Equipe-Botcem/Seguidor_Lampedrao/Estrutura/bateria.SLDPRT

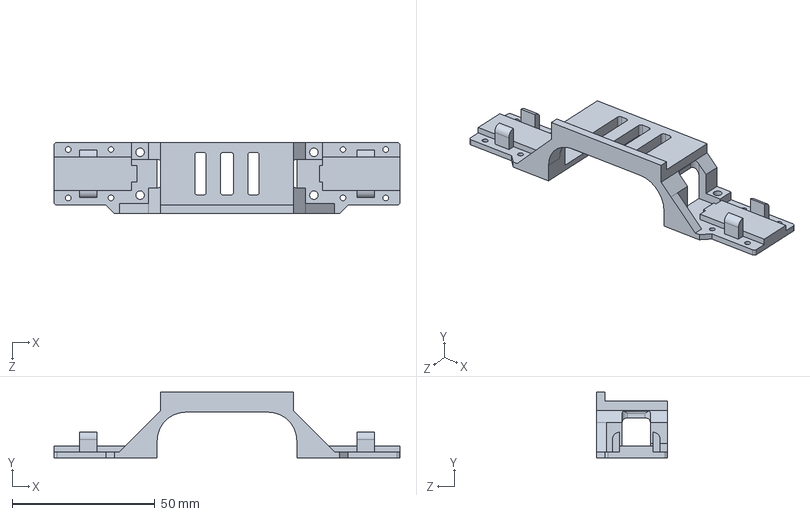
[picture p15: CAD file, 2023-05-12]
Estrutura/bateria.SLDPRT
121.4 x 23.0 x 25.0 mm
