Equipe-Botcem/Seguidor_Lampedrao/Elétrica/parts/1622242-1/1622242-1.step

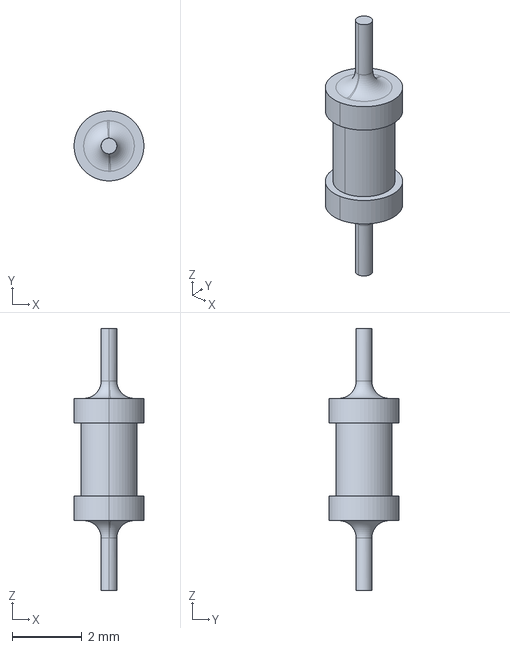
[picture p16: CAD file, 2023-05-12]
Elétrica/parts/1622242-1/1622242-1.step
2.00 x 2.00 x 7.50 mm
