Equipe-Botcem/Seguidor_Lampedrao/esp32_code/include/Sensor.h

#ifndef _SENSOR_
#define _SENSOR_
#define RESOLUTION 4095
#include "Arduino.h"

class Sensor
{
public:
	Sensor();
	Sensor(unsigned char pin);

	void Init();

	uint16_t Read_sensor();
	int Read_Calibrado();
	bool Read_histerese();

	void setAngle(float angulo);
	void find_max();	
	float Read_CalibradoPonderado();
	float GetMax();


	float Cmax = 0;
	float Cmin = 0;
	
	
private:
	unsigned char pin_sensor;
	float angle;

	enum estado{
		Preto = 0,
		Branco
	};

	estado ant = Preto;
};

#endif
