Equipe-Botcem/Seguidor_Lampedrao/esp32_code/src/Controlador.cpp

#include "Controlador.h"
#include "Arduino.h"

Controlador::Controlador(){

}

void Controlador::setKp(float kp){
    Kp = kp;
}

void Controlador::setKd(float kd){
    Kd = kd;
}

void Controlador::setKi(float ki){
    Ki = ki;
}

void Controlador::setControlador(float kp, float kd, float ki){
    setKp(kp);
    setKd(kd);
    setKi(ki);
}   

float Controlador::calcPID(float erro){

    float temp = atuation_k1 + (Kp + Ki + Kd)*erro + (Ki - Kp - 2*Kd)*erro_k1 + Kd*erro_k2;

    atuation_k1 = temp;

    erro_k2 = erro_k1;
    erro_k1 = erro;

    return temp;
}

float Controlador::getAmostragem(){
    return tempo_amostragem;
}


void Controlador::resetConditions(){
    erro_k1 = 0;
    erro_k2 = 0;
    atuation_k1 = 0;
}

void Controlador::teste(float erro){
    Serial.print("PID: ");
    Serial.println(calcPID(erro));
}
